christrotter/ultrafalcon/images/bad-led-footprint.jpg

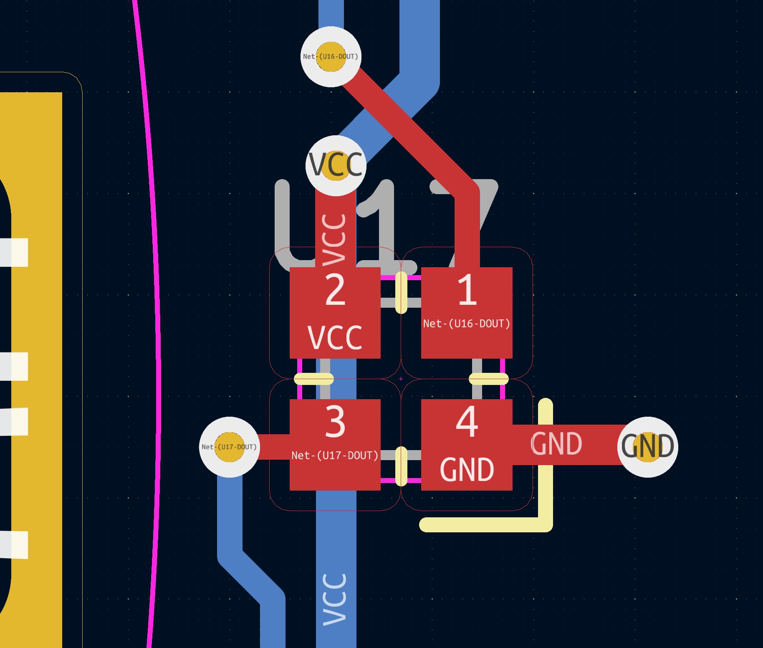
images/bad-led-footprint.jpg
