christrotter/ultrafalcon/images/falcon-pcb.jpg

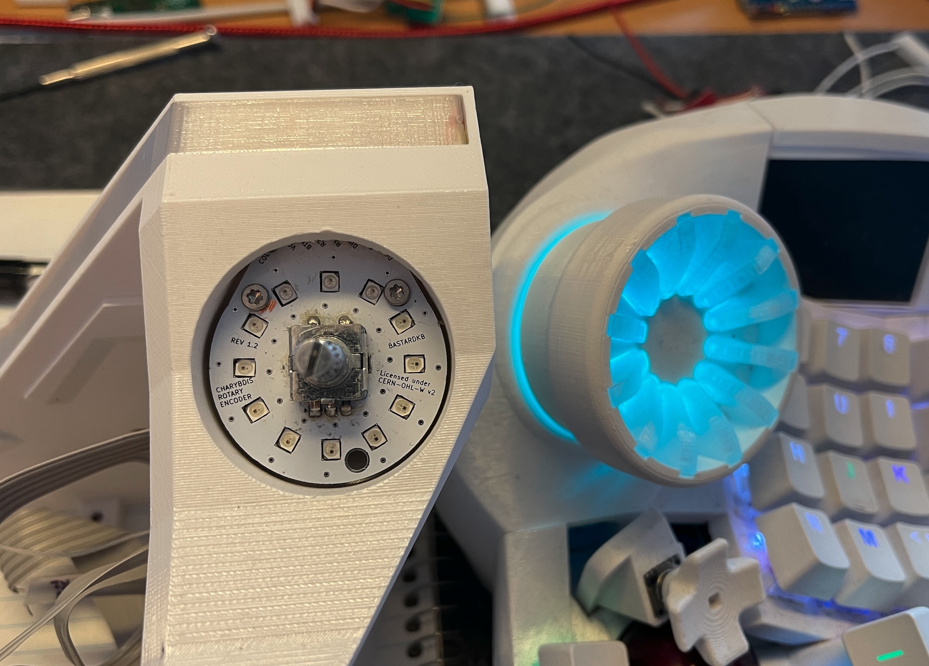
images/falcon-pcb.jpg
