christrotter/ultrafalcon/images/switch-modeling.jpg

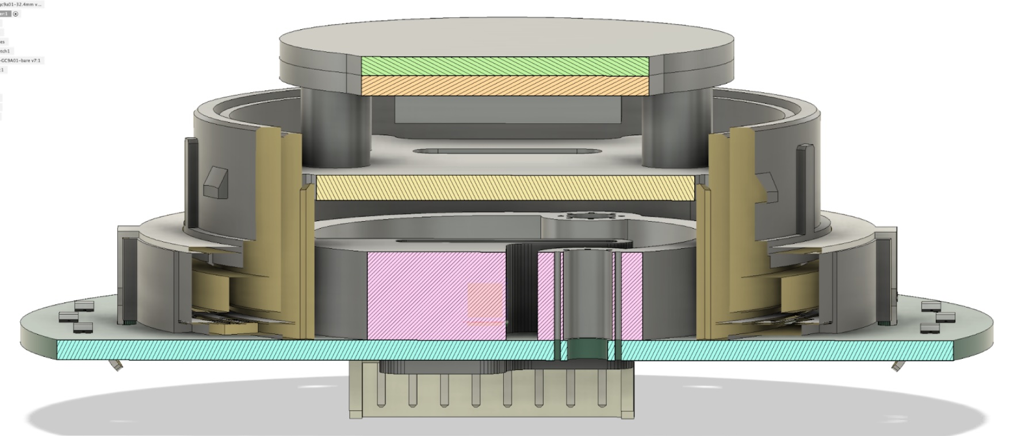
images/switch-modeling.jpg
