christrotter/ultrafalcon/images/uf-pcb-layout.jpg

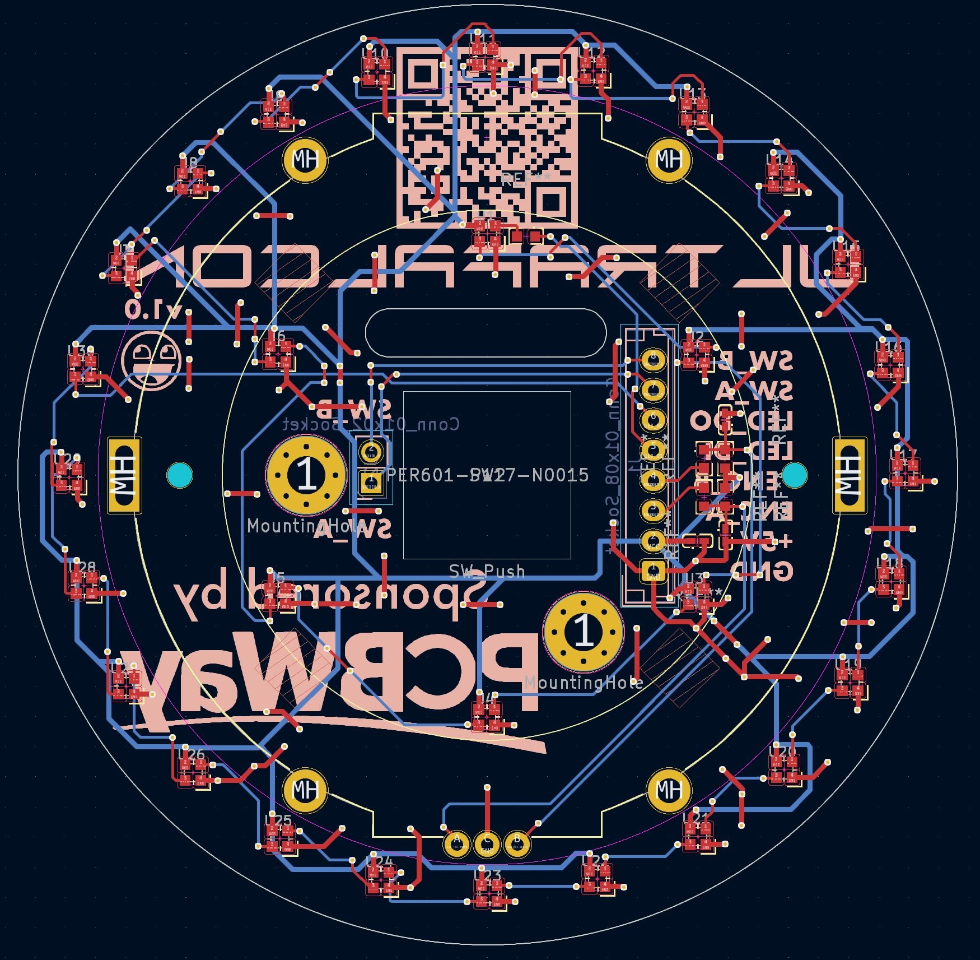
images/uf-pcb-layout.jpg
