christrotter/ultrafalcon/images/image-as-manufactured2.jpg

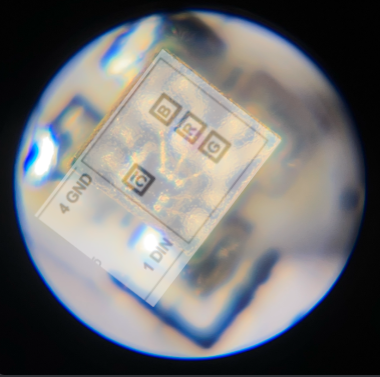
images/image-as-manufactured2.jpg
